tomtominator/Streets-of-Rodeo-Lap-Timer/images/PXL_20220809_234728932.jpg

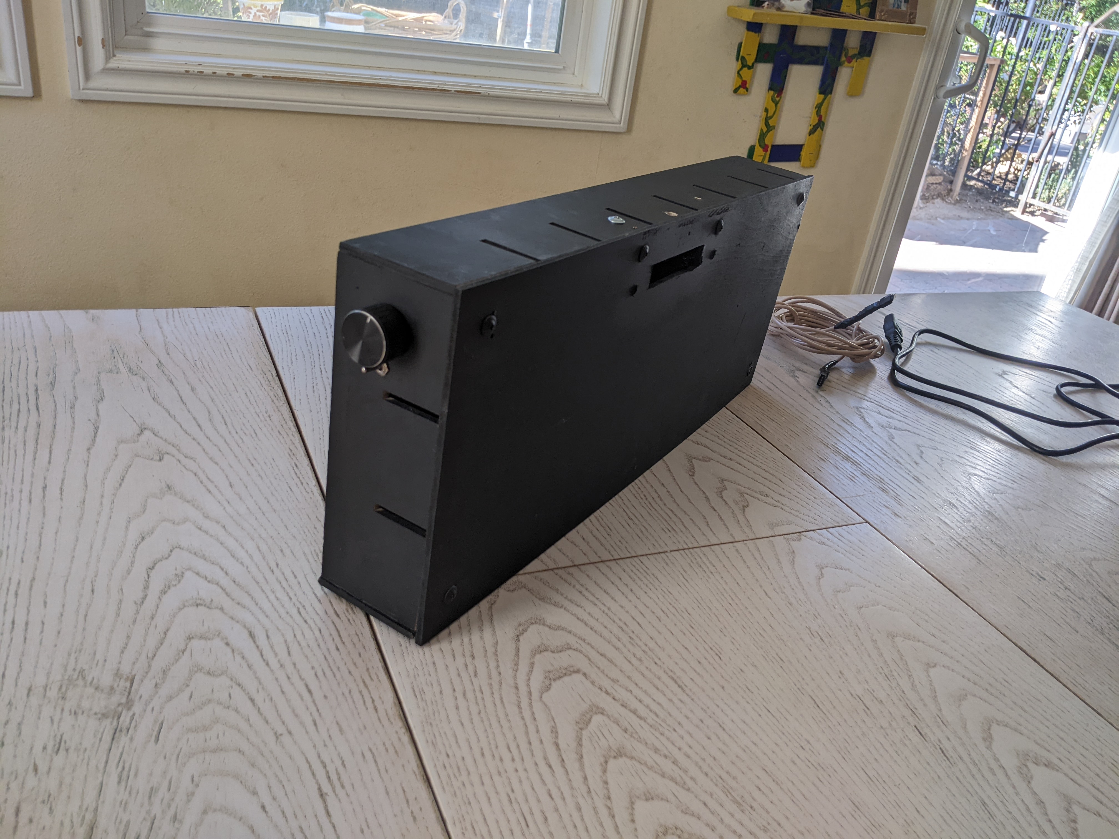
images/PXL_20220809_234728932.jpg
