tomtominator/Streets-of-Rodeo-Lap-Timer/images/PXL_20220809_234743986.jpg

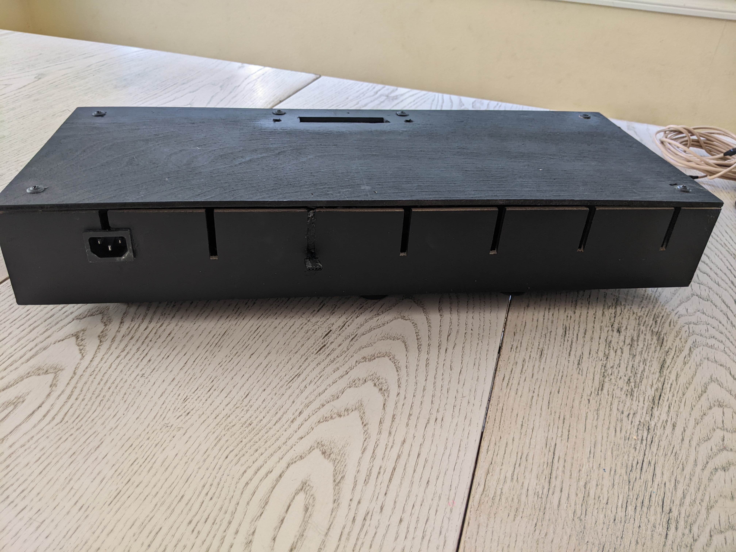
images/PXL_20220809_234743986.jpg
